SolderedElectronics/CAN-Transceiver-MCP2518-board-hardware-design/OUTPUTS/V1.1.1/333020.jpg

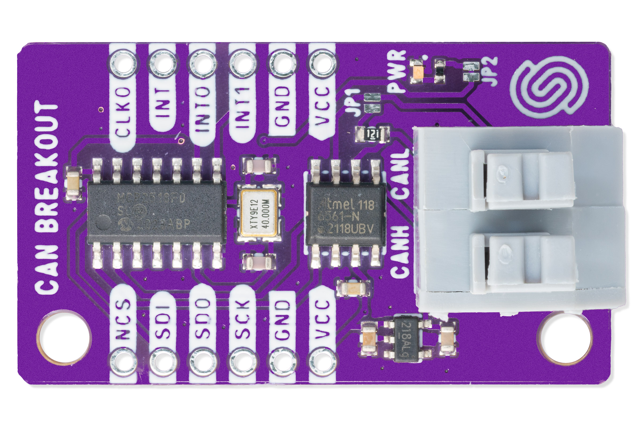
OUTPUTS/V1.1.1/333020.jpg
