SolderedElectronics/CAN-Transceiver-MCP2518-board-hardware-design/OUTPUTS/V1.1.1/CAN Transceiver MCP2518 board Pinout.jpg

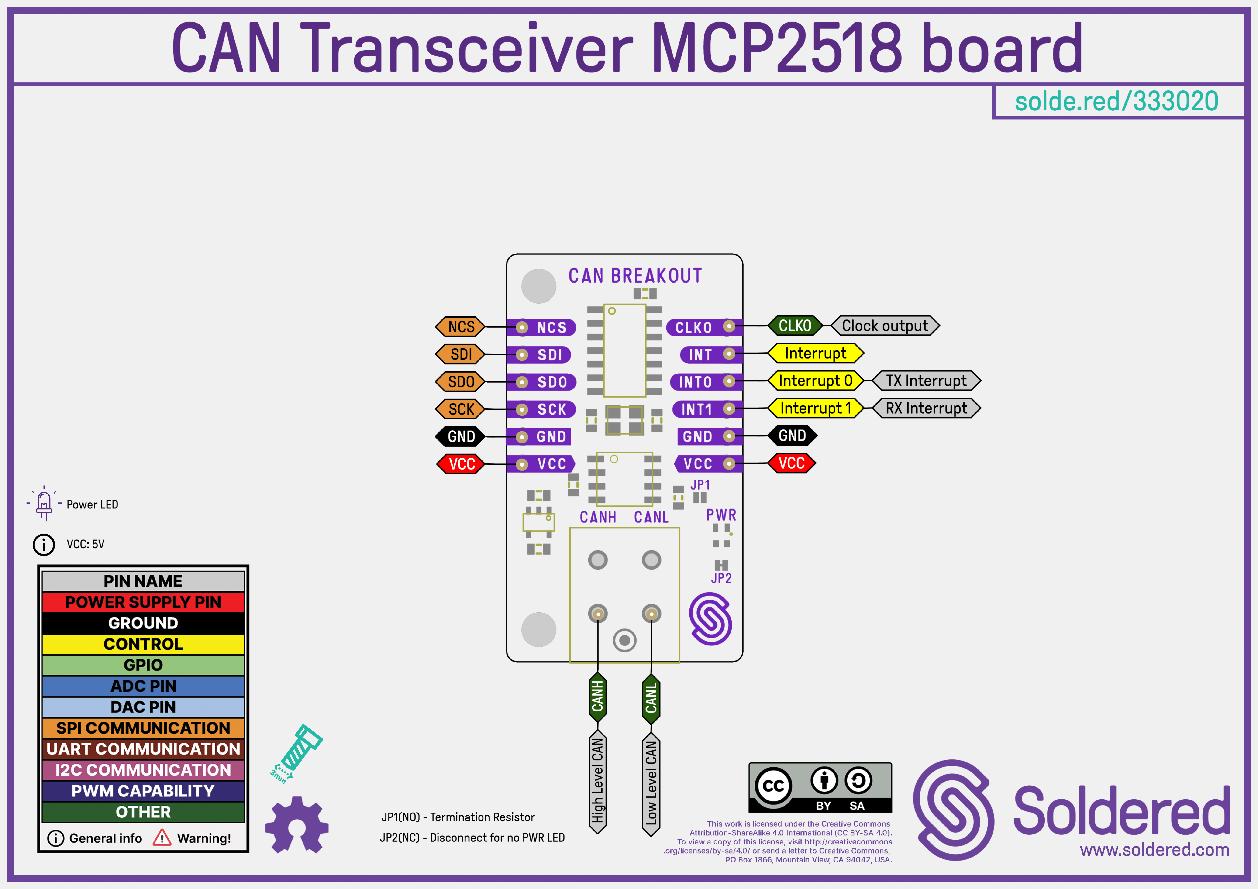
OUTPUTS/V1.1.1/CAN Transceiver MCP2518 board Pinout.jpg
